Mint9821/SCH16T_Evt_Board/Charging_Circuit_LTSpice/USB_and_LiPo.asc

D2: zener
M2: pmos
R1: res; 100k
V1: voltage; 5
V2: voltage; 3.7
Named nets: OUTPUT, 0
USB VBAT
LiPo
.tran 1
BatteryIC
V(n001)
